Maddca/DC_To_DC_Converter/Images/Portable Battery Phone Charger.png

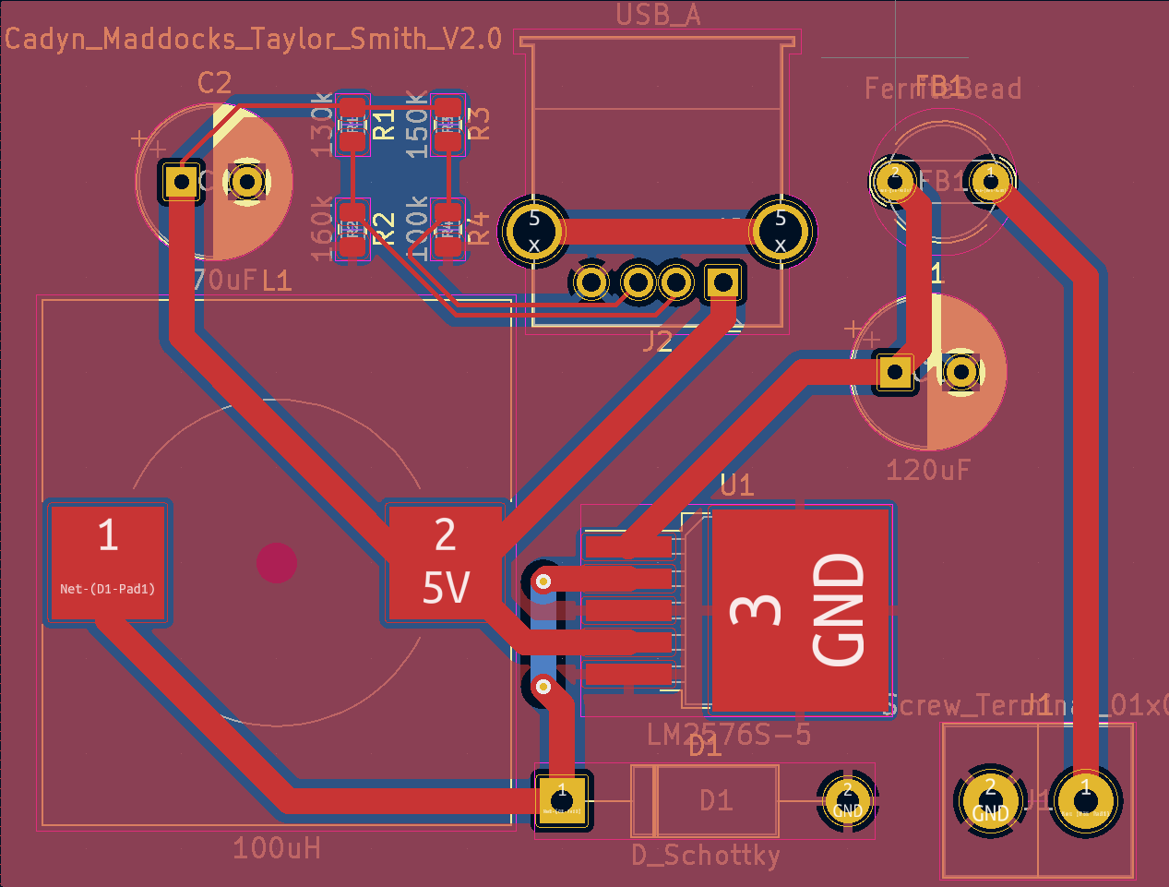
Images/Portable Battery Phone Charger.png
