Maddca/DC_To_DC_Converter/Images/RESULTS-3.jpg

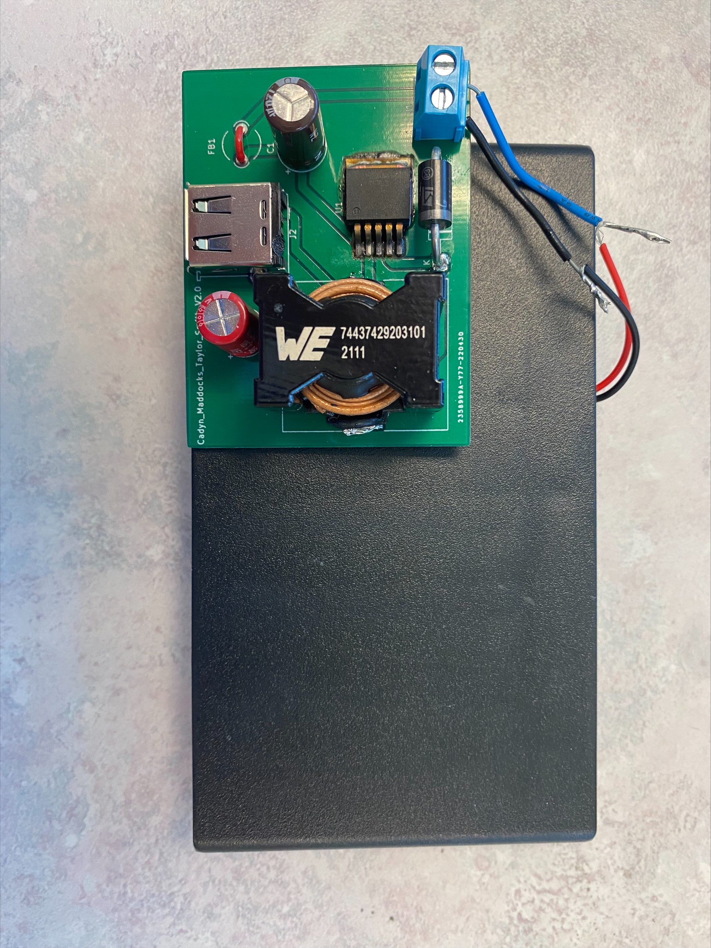
Images/RESULTS-3.jpg
