Maddca/DC_To_DC_Converter/Images/RESULTSWCURRENT.png

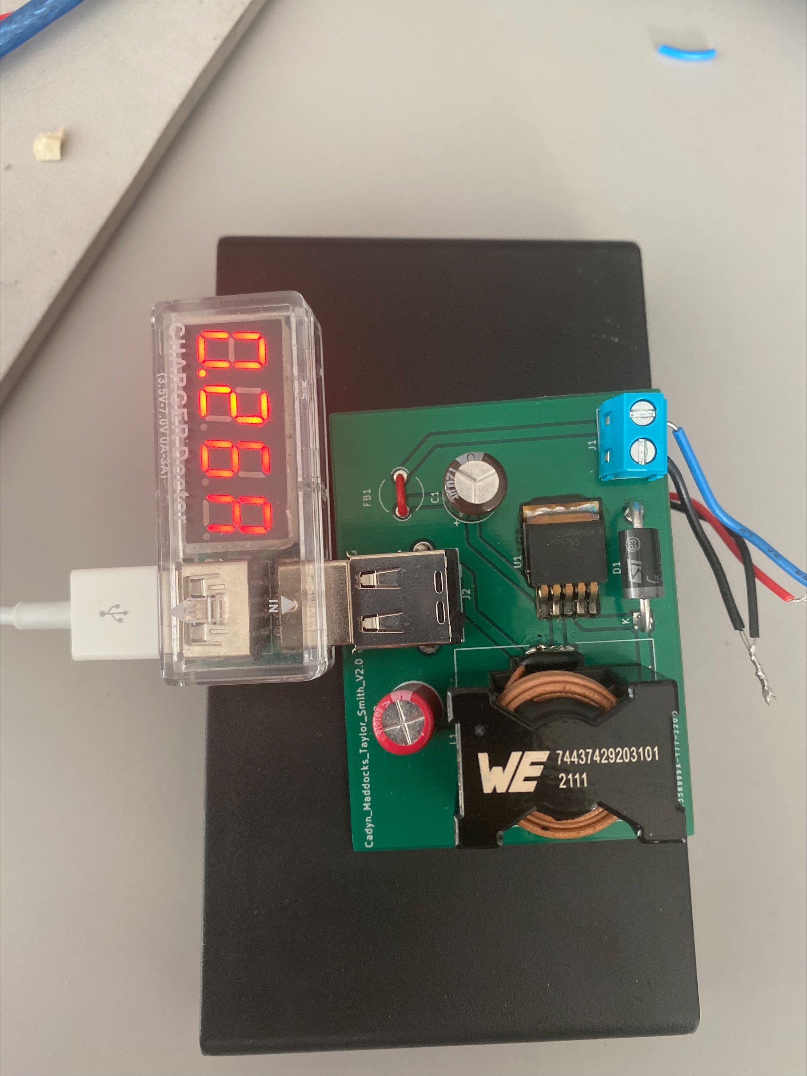
Images/RESULTSWCURRENT.png
